simont77/PowerShield/Astroberry_assembly_ISO_back_section.png

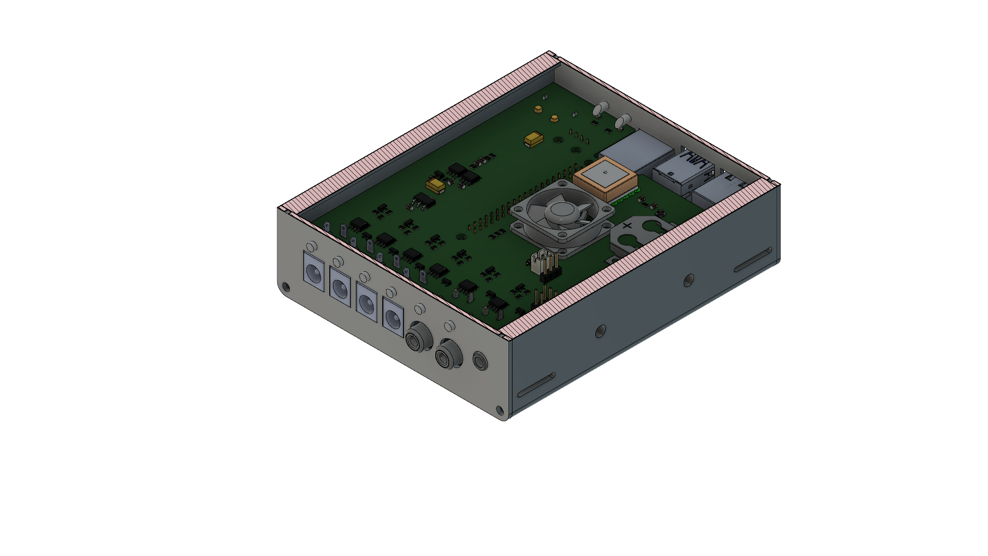
Astroberry_assembly_ISO_back_section.png
