simont77/PowerShield/ECAD/pics/Astroberry_assembled_PCB_back.png

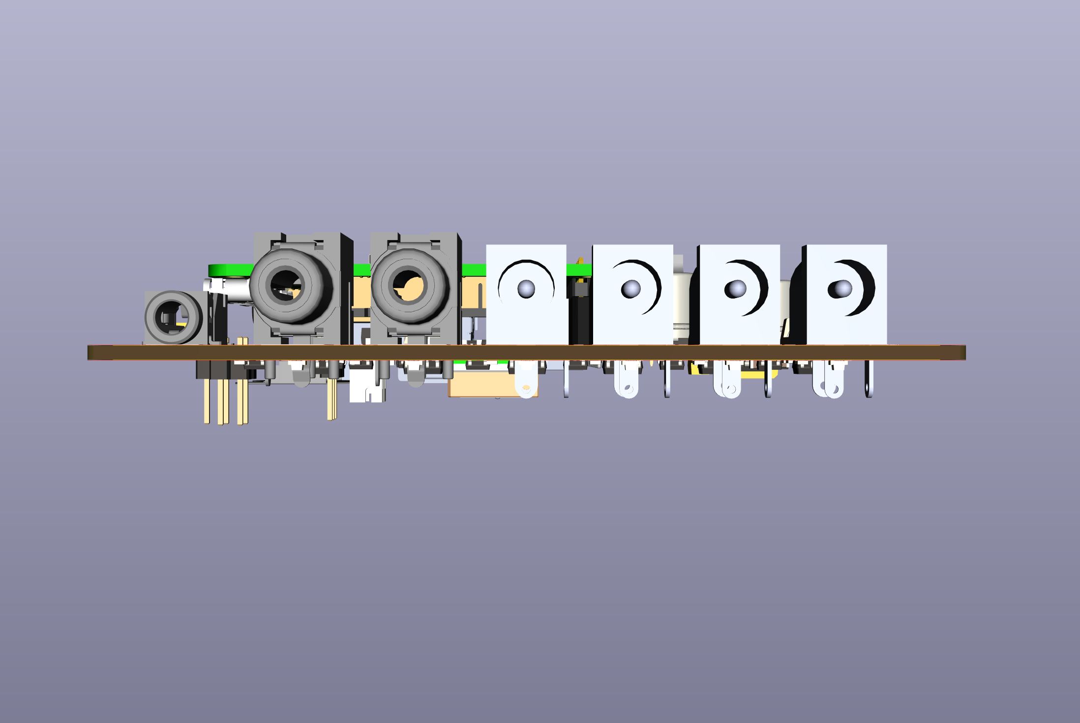
ECAD/pics/Astroberry_assembled_PCB_back.png
