simont77/PowerShield/ECAD/pics/Astroberry_assembled_PCB_left.png

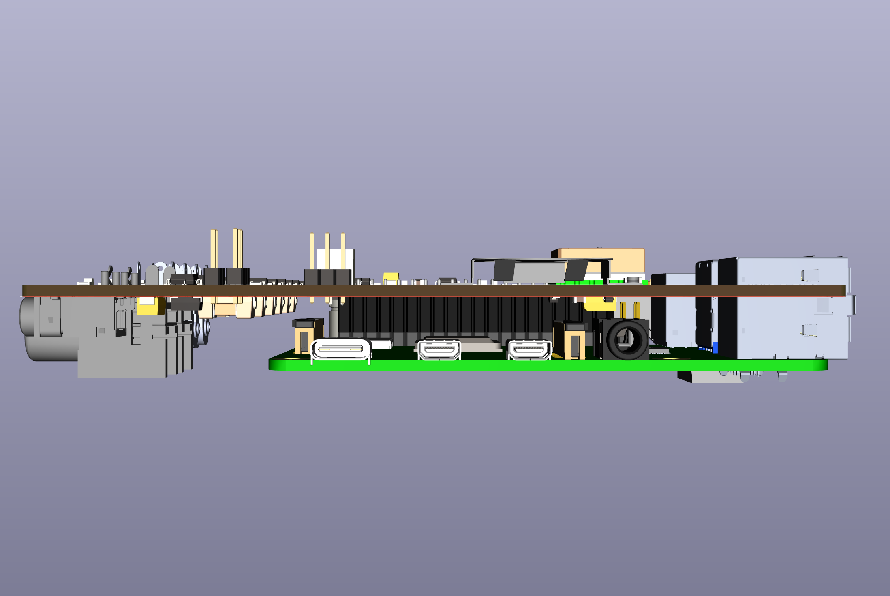
ECAD/pics/Astroberry_assembled_PCB_left.png
