simont77/PowerShield/ECAD/pics/Astroberry_assembled_PCB_right.png

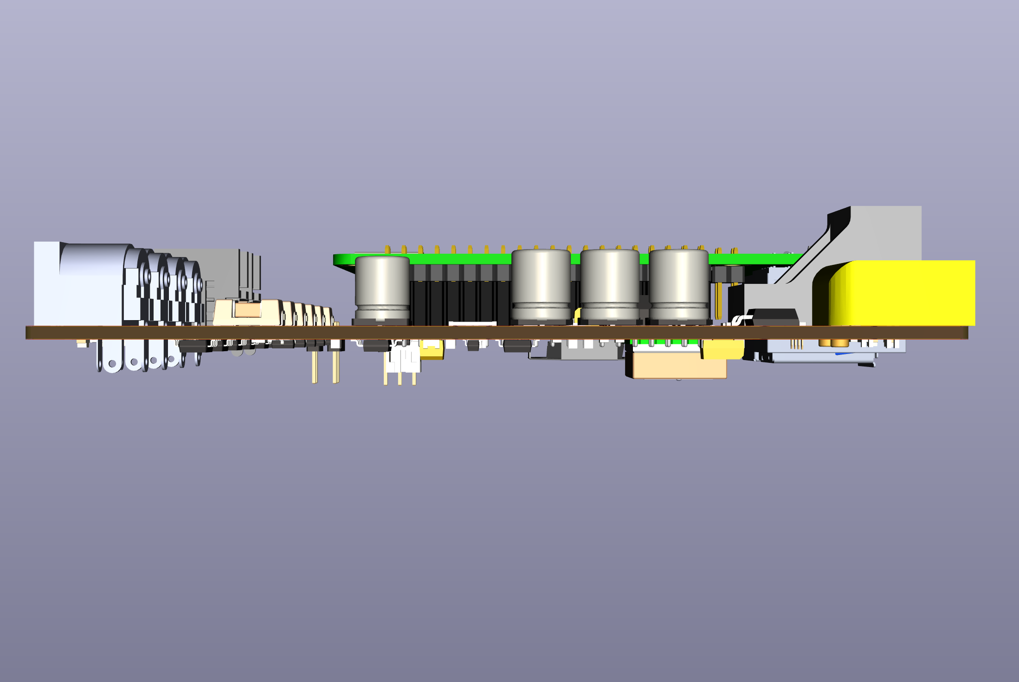
ECAD/pics/Astroberry_assembled_PCB_right.png
